tebl/RC2014/Gallery/rc2014_cold_or_warm.PNG

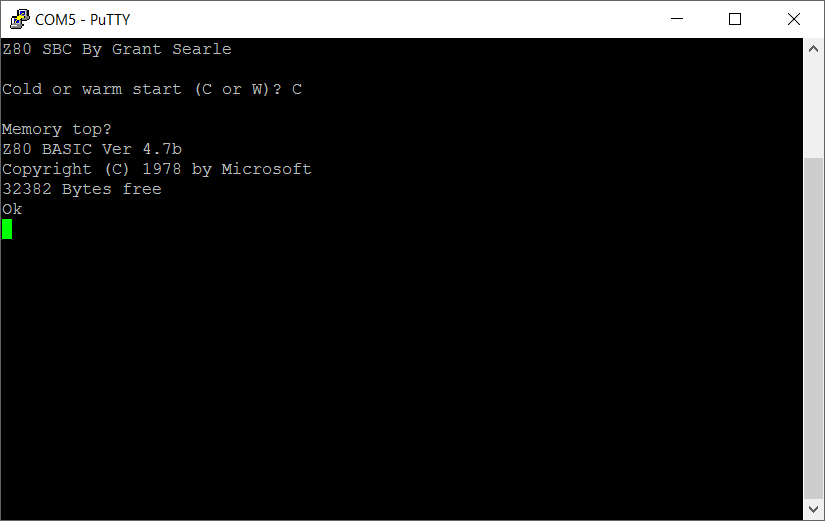
Gallery/rc2014_cold_or_warm.PNG
