tebl/RC2014/RC2014 IDE/gallery/CF Sandisk Basic (updated).PNG

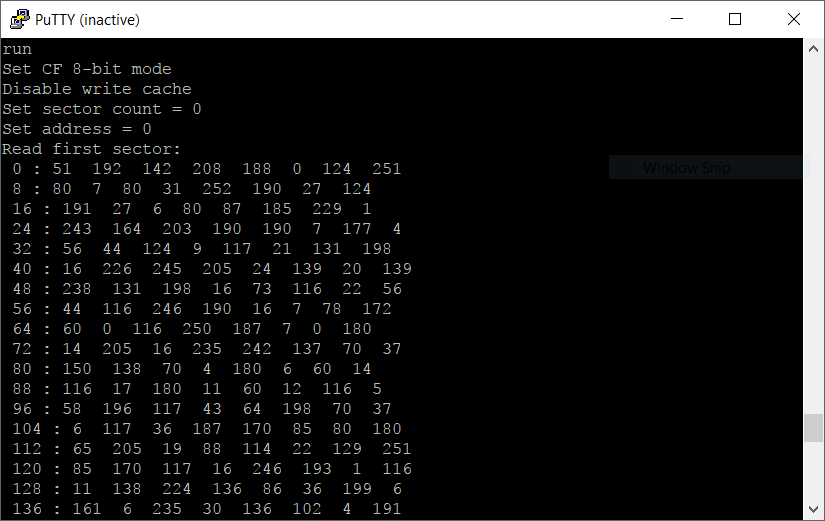
RC2014 IDE/gallery/CF Sandisk Basic (updated).PNG
