tebl/RC2014/RC2014 Tandy Sound Card/gallery/pcb.png

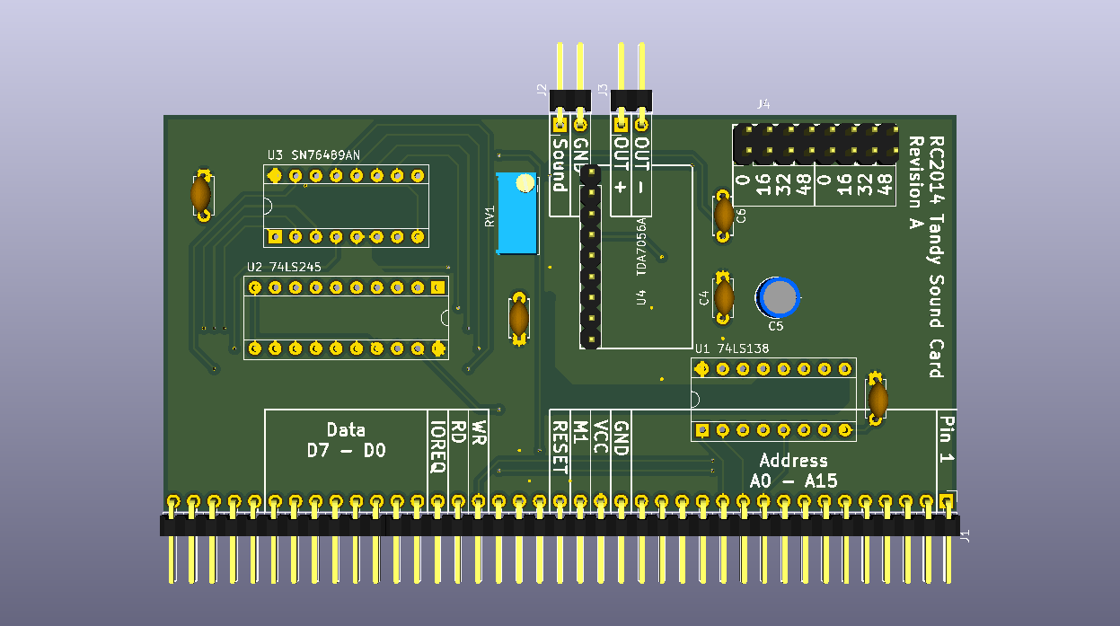
RC2014 Tandy Sound Card/gallery/pcb.png
